sb-ocr/ocreeb-mk-2/Modules/Faders/CAD/STLs/Ocreeb_fader_knob.stl

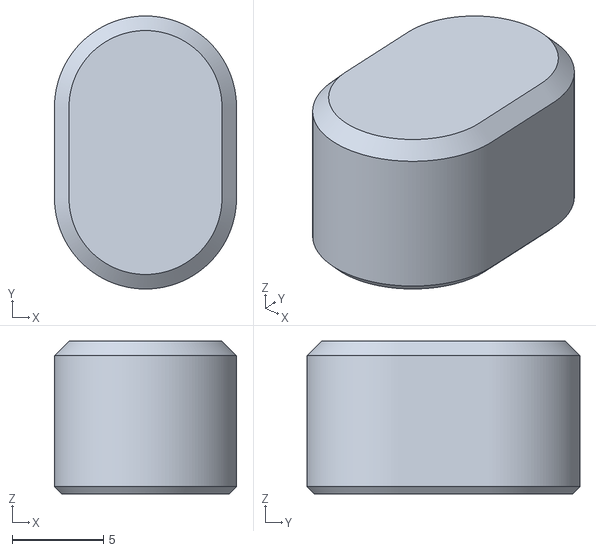
[picture p15: CAD file, 2024-01-15]
Modules/Faders/CAD/STLs/Ocreeb_fader_knob.stl
10.0 x 15.0 x 8.40
