sb-ocr/ocreeb-mk-2/Macropad/CAD/STLs/Ocreeb_core_middle.stl

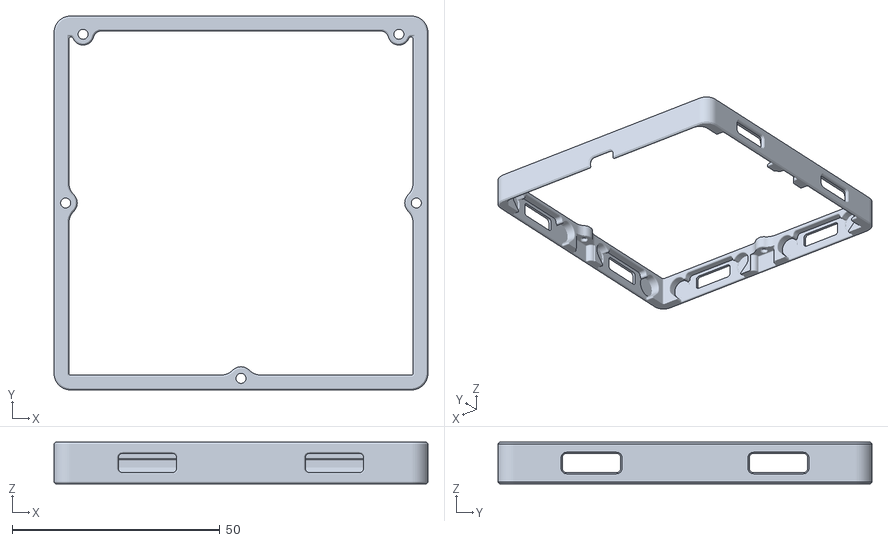
[picture p16: CAD file, 2024-01-15]
Macropad/CAD/STLs/Ocreeb_core_middle.stl
90.0 x 90.0 x 10.0
