sb-ocr/ocreeb-mk-2/Macropad/CAD/STLs/Ocreeb_core_bottom.stl

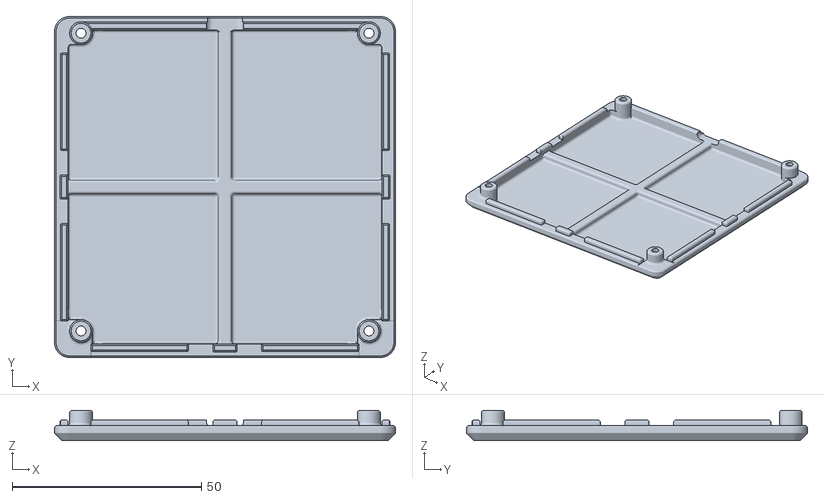
[picture p17: CAD file, 2024-01-15]
Macropad/CAD/STLs/Ocreeb_core_bottom.stl
90.0 x 90.0 x 8.02
